FranckLab/Intermediate-Rate-Tension-Device/Device 3D Printed Parts/TensionDevice - Sample Dish Holder.step

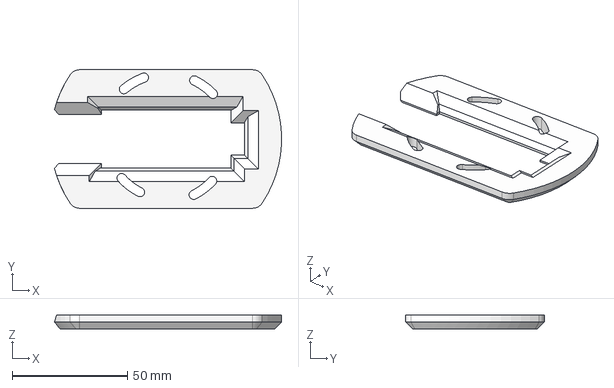
[picture p15: CAD file, 2022-11-29]
Device 3D Printed Parts/TensionDevice - Sample Dish Holder.step
98.3 x 60.0 x 6.00 mm
