FranckLab/Intermediate-Rate-Tension-Device/Device Purchased Parts/8381K3 - Rail.step

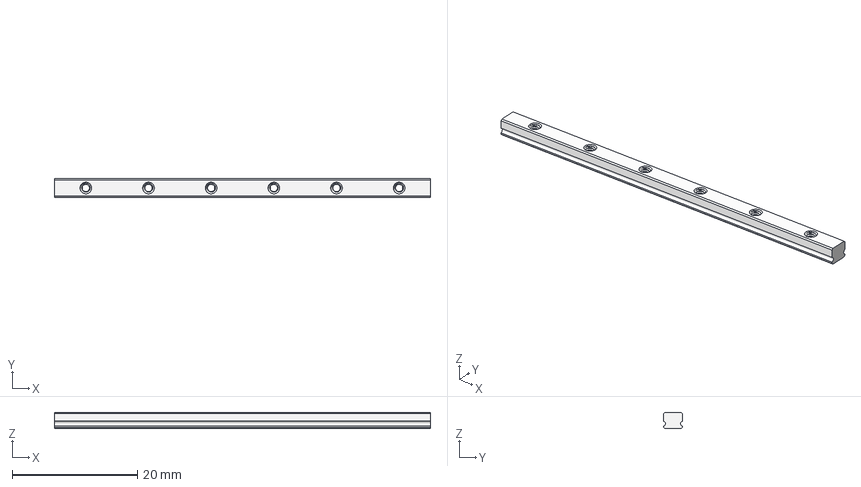
[picture p16: CAD file, 2022-11-29]
Device Purchased Parts/8381K3 - Rail.step
60.0 x 3.00 x 2.60 mm
