FranckLab/Intermediate-Rate-Tension-Device/Samples/7mm Hydrogel - Sample Mold.step

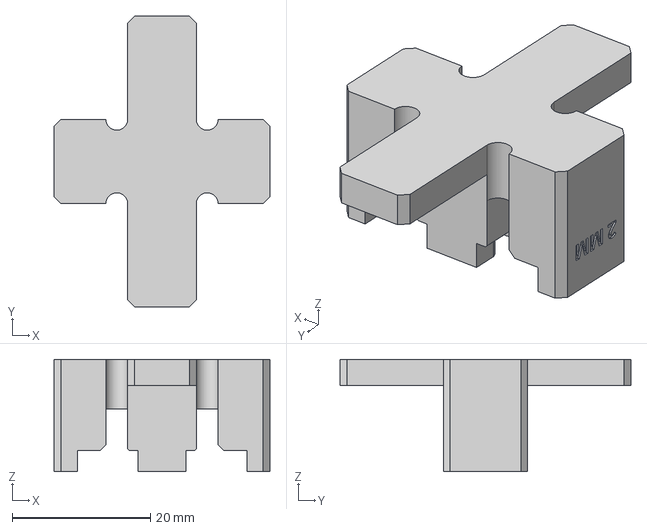
[picture p17: CAD file, 2022-11-29]
Samples/7mm Hydrogel - Sample Mold.step
31.2 x 42.0 x 16.2 mm
