FranckLab/Intermediate-Rate-Tension-Device/Waterjet Cut Aluminum Parts/TensionDevice_Nikon Baseplate Mount.step

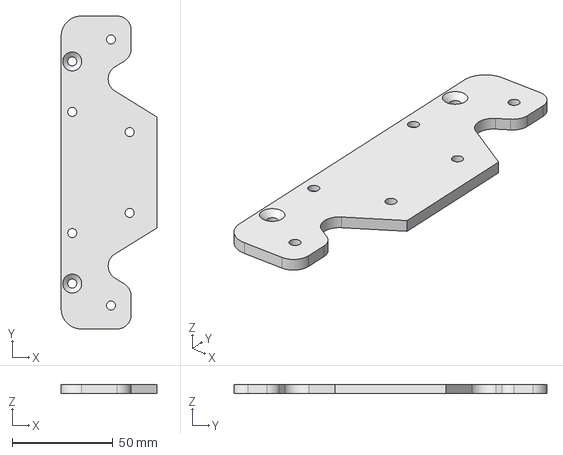
[picture p18: CAD file, 2022-11-29]
Waterjet Cut Aluminum Parts/TensionDevice_Nikon Baseplate Mount.step
47.4 x 155.0 x 4.59 mm
