FranckLab/Intermediate-Rate-Tension-Device/Compression Modifications/Compression - Sample Mold Side.step

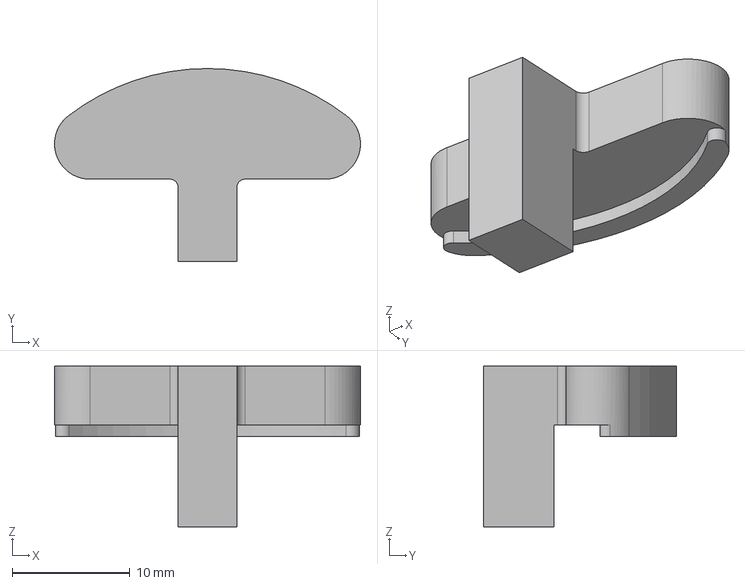
[picture p19: CAD file, 2022-11-29]
Compression Modifications/Compression - Sample Mold Side.step
26.0 x 16.4 x 13.7 mm
