FranckLab/Intermediate-Rate-Tension-Device/Device 3D Printed Parts/Timing Belt Tensioner.step

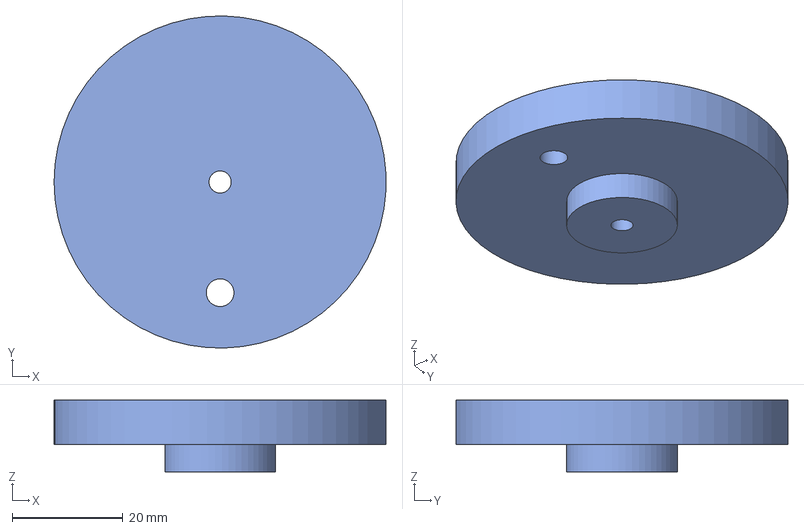
[picture p20: CAD file, 2022-11-29]
Device 3D Printed Parts/Timing Belt Tensioner.step
60.0 x 60.0 x 13.0 mm
