FranckLab/Intermediate-Rate-Tension-Device/Device Purchased Parts/BESTORQ 620-5M-9 5M Timing Belt.step

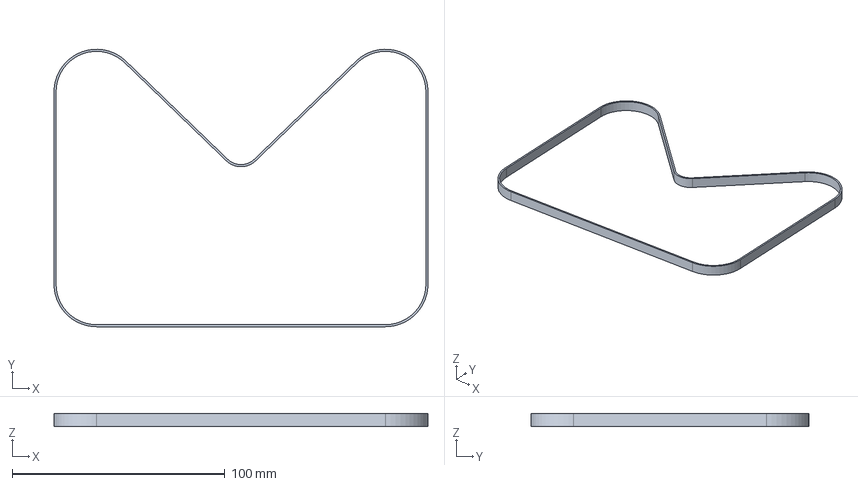
[picture p21: CAD file, 2022-11-29]
Device Purchased Parts/BESTORQ 620-5M-9 5M Timing Belt.step
176.0 x 130.6 x 6.00 mm
