FranckLab/Intermediate-Rate-Tension-Device/Samples/10mm PDMS Sample - M_Gripper.step

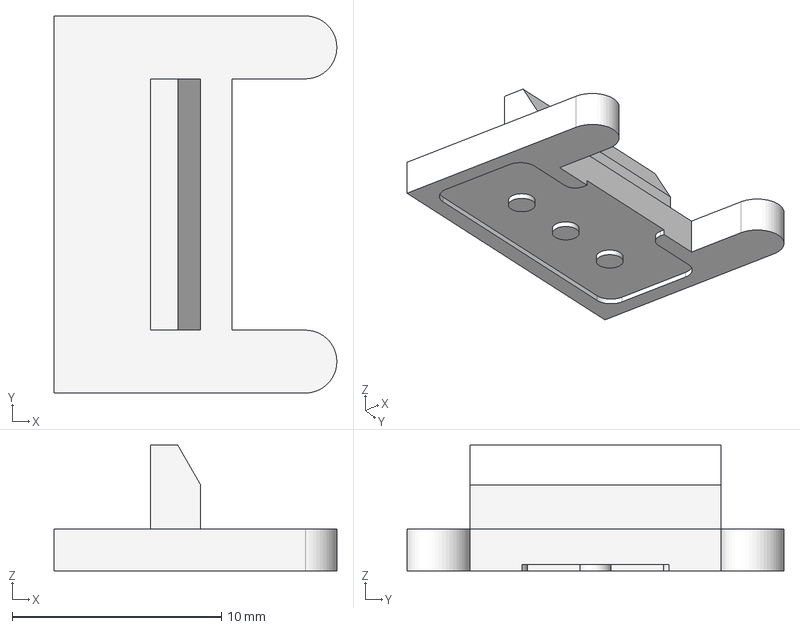
[picture p22: CAD file, 2022-11-29]
Samples/10mm PDMS Sample - M_Gripper.step
13.5 x 18.0 x 6.00 mm
