FranckLab/Intermediate-Rate-Tension-Device/Compression Modifications/Compression - Rail Mount (One Motor).step

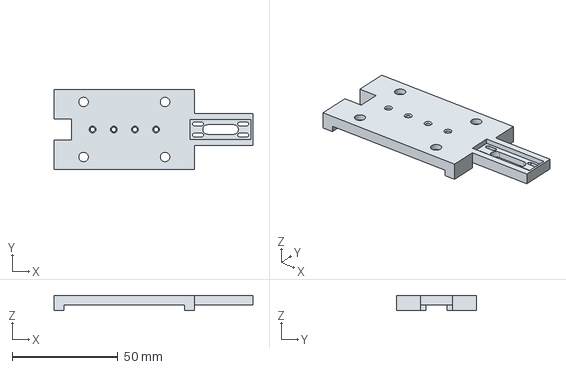
[picture p23: CAD file, 2022-11-29]
Compression Modifications/Compression - Rail Mount (One Motor).step
94.0 x 38.0 x 7.00 mm
