FranckLab/Intermediate-Rate-Tension-Device/Device Purchased Parts/T8 Pillow Block Bearing (MOTOU 0791300576783).step

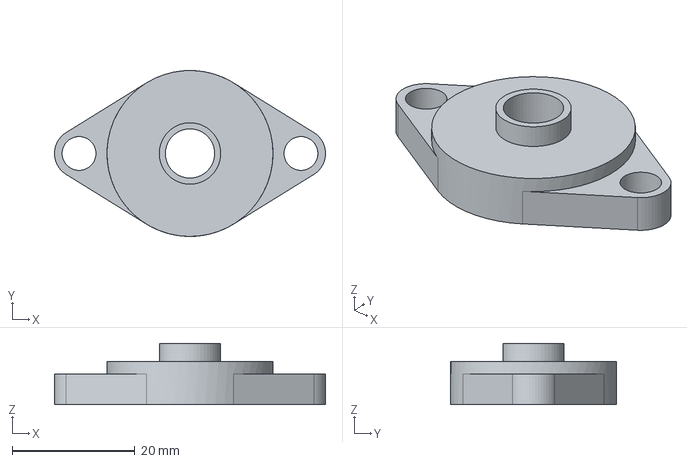
[picture p24: CAD file, 2022-11-29]
Device Purchased Parts/T8 Pillow Block Bearing (MOTOU 0791300576783).step
44.1 x 27.0 x 10.0 mm
