FranckLab/Intermediate-Rate-Tension-Device/Samples/7mm Hydrogel Mold - F-Grip.step

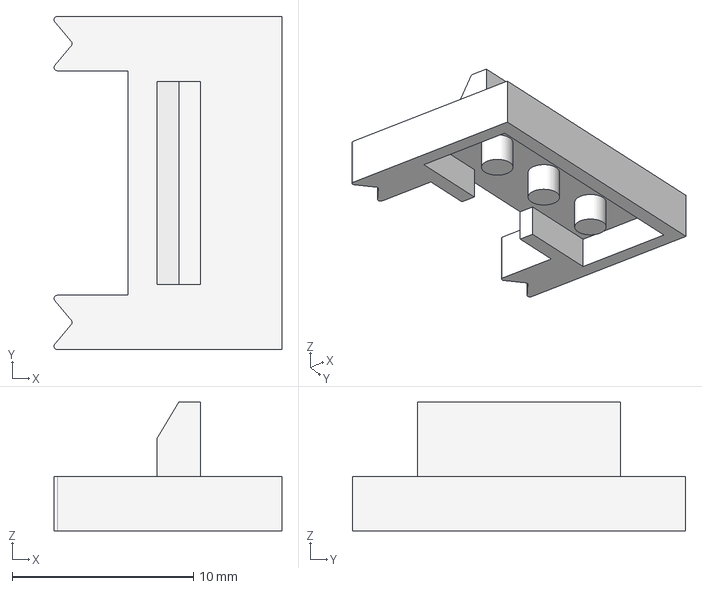
[picture p25: CAD file, 2022-11-29]
Samples/7mm Hydrogel Mold - F-Grip.step
12.6 x 18.4 x 7.12 mm
