FranckLab/Intermediate-Rate-Tension-Device/Compression Modifications/Compression - Sample Mold Base.step

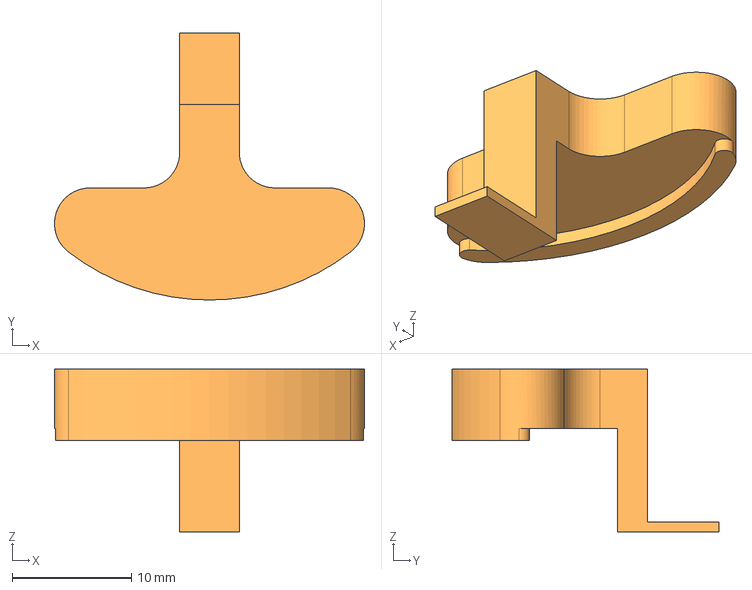
[picture p26: CAD file, 2022-11-29]
Compression Modifications/Compression - Sample Mold Base.step
26.0 x 22.4 x 13.7 mm
