FranckLab/Intermediate-Rate-Tension-Device/Samples/10mm PDMS Sample - F_Gripper.step

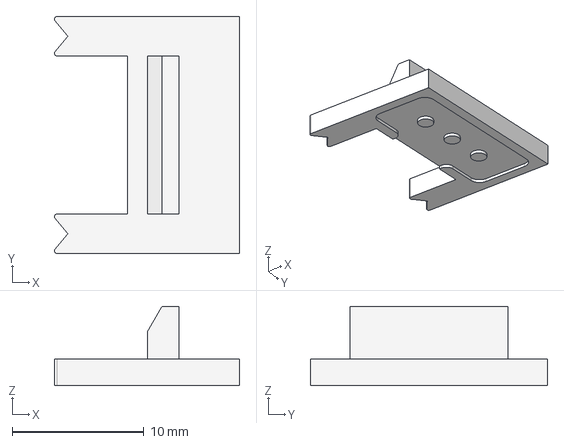
[picture p27: CAD file, 2022-11-29]
Samples/10mm PDMS Sample - F_Gripper.step
14.1 x 18.0 x 6.00 mm
