FranckLab/Intermediate-Rate-Tension-Device/Compression Modifications/Compression - Impact Grip.step

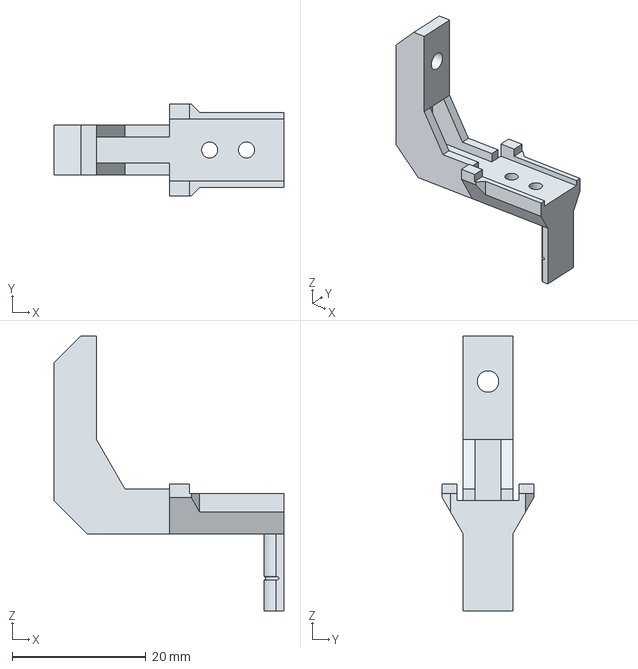
[picture p28: CAD file, 2022-11-29]
Compression Modifications/Compression - Impact Grip.step
34.3 x 13.7 x 41.1 mm
