FranckLab/Intermediate-Rate-Tension-Device/Samples/7mm Hydrogel Mold - M-Grip.step

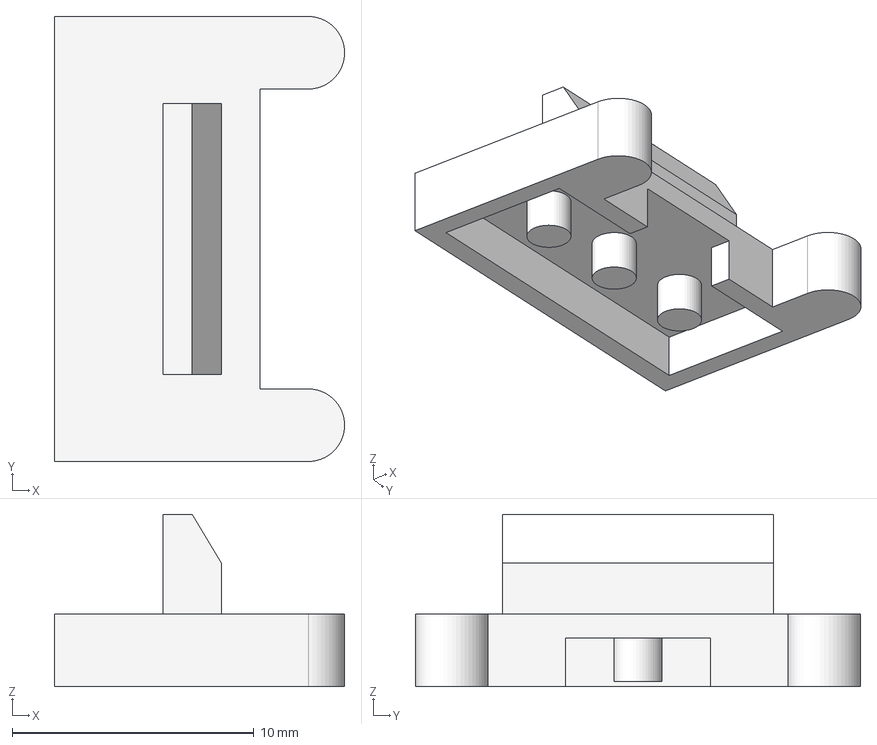
[picture p29: CAD file, 2022-11-29]
Samples/7mm Hydrogel Mold - M-Grip.step
12.0 x 18.4 x 7.12 mm
