FranckLab/Intermediate-Rate-Tension-Device/Compression Modifications/Compression Sample - Stamp_Hamburger.step

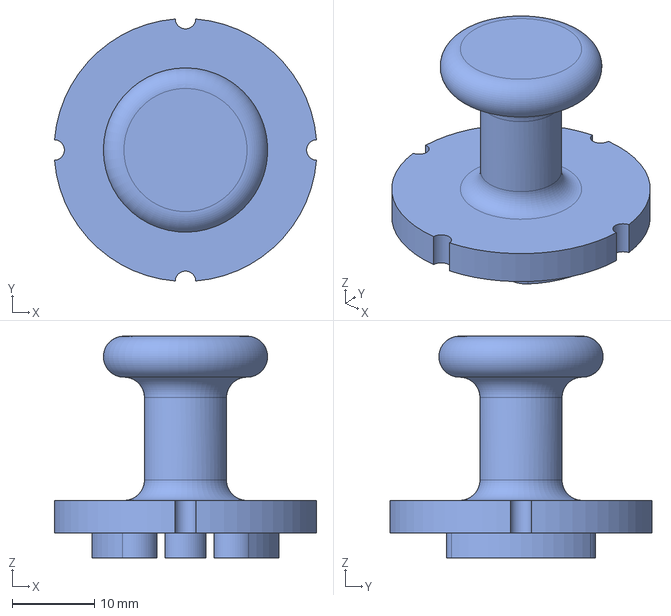
[picture p30: CAD file, 2022-11-29]
Compression Modifications/Compression Sample - Stamp_Hamburger.step
31.9 x 31.9 x 27.0 mm
