FranckLab/Intermediate-Rate-Tension-Device/Compression Modifications/Compression - Sample Holder Cap.step

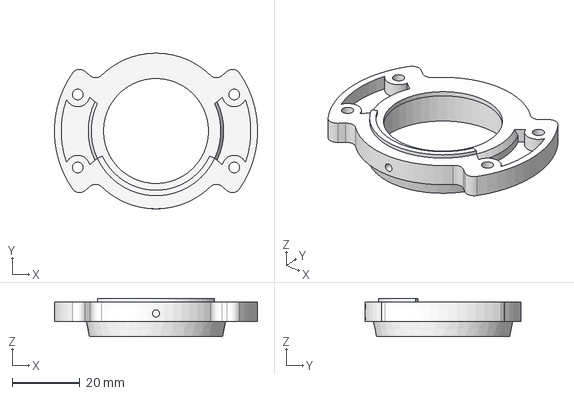
[picture p31: CAD file, 2022-11-29]
Compression Modifications/Compression - Sample Holder Cap.step
59.9 x 46.0 x 11.3 mm
