FranckLab/Intermediate-Rate-Tension-Device/Compression Modifications/Compression - Baseplate for 155mm x 185mm Stage.step

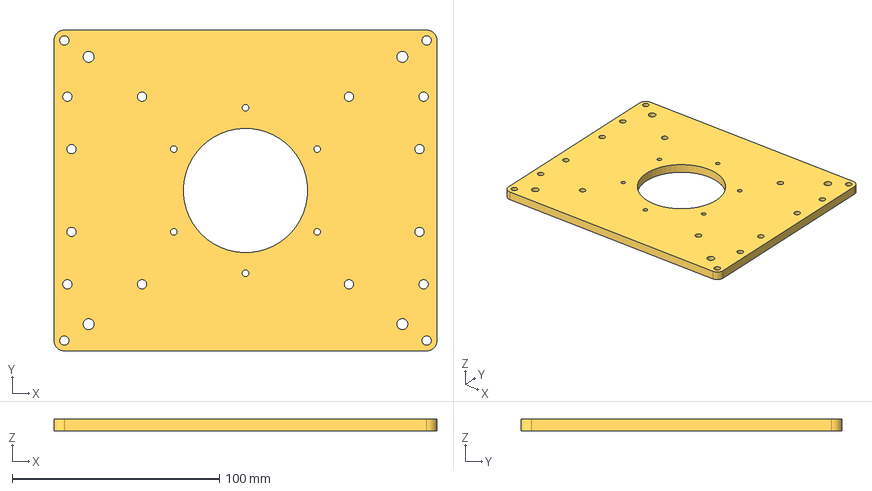
[picture p32: CAD file, 2022-11-29]
Compression Modifications/Compression - Baseplate for 155mm x 185mm Stage.step
185.0 x 155.0 x 6.00 mm
